flamerten/EinkWeatherMonitor/src/USB_C.jpg

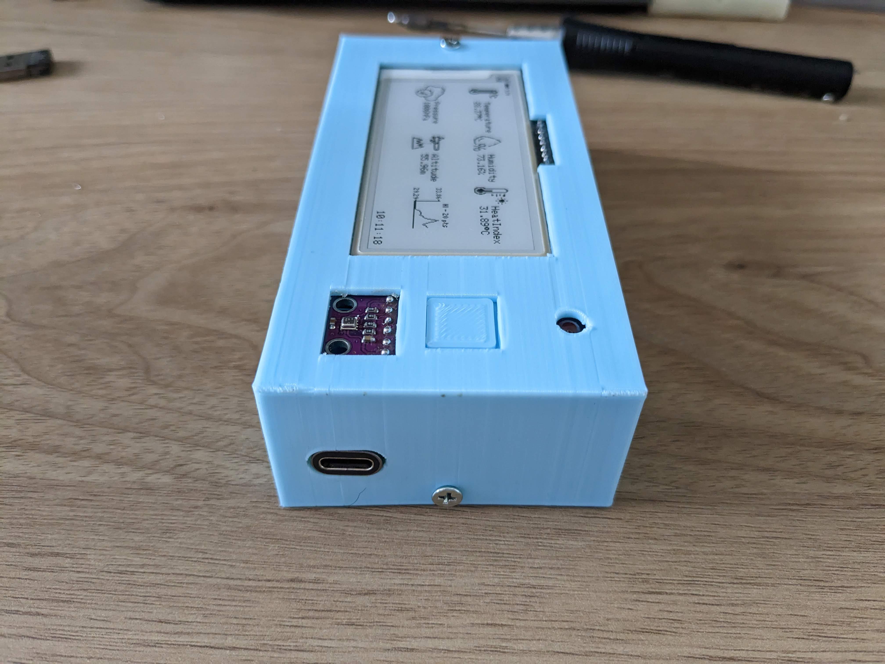
src/USB_C.jpg
